bstrobel/Cass2SD/LTSpice/Cass2SD_AnalogStage.asc

C1: cap; 100n
C2: cap; 1n
C4: cap; 1.5p
C5: cap; 10p
C6: cap; 10p
D1: diode; 1N4148
D2: diode; 1N4148
R1: res; 15
R2: res; 1Meg
R3: res; 70k
R4: res; 30k
R5: res; 10Meg
R6: res; 100k
R7: res; 470
R8: res; 33k
R9: res; 13k
R11: res; 10Meg
U1: UniversalOpamp2; ""
U2: UniversalOpamp2; ""
V1: voltage; PULSE(3.2 0.2 2m 35n 35n .25m .5m 500); Rser=.5
V2: voltage; 5; Rser=.1
Named nets: 0, OUT, IN, NonInv_U1, TTL, Virtual_GND, VCC
.tran 0 100m 0m
.inc LM358.sub
Z9001 output circuit
1
2
3
5
6
7
8
4
ATMega input stage
