bstrobel/Cass2SD/main/kc_cass_common.c

/*
 * kc_cass_format_def.c
 *
 * Created: 06.06.2017 19:27:29
 *  Author: Bernd
 */ 
#define __PROG_TYPES_COMPAT__
#include <avr/pgmspace.h>
#include <avr/interrupt.h>
#include <avr/sfr_defs.h>
#include <stdbool.h>
#include <string.h>
#include <util/delay.h>
#include "../ff_avr/ff.h"
#include "../ff_avr/diskio.h"
#include "../ff_avr/xitoa.h"
#include "../lcd/lcd.h"
#include "debounced_keys.h"
#include "display_util.h"
#include "kc_cass_common.h"

DIR Dir;			/* http://elm-chan.org/fsw/ff/00index_e.html */
FILINFO Finfo;
FRESULT fr;
FATFS FatFs;		/* File system object for each logical drive */
FIL fhdl;

uint16_t disp_timer = 0;
bool is_file_details_displayed = false;

uint8_t* start_buf_ptr = buf;
uint8_t block_len = 128;
KC_FILE_TYPE kc_file_type = RAW;
uint8_t number_of_blocks = 0;

SYSTEM_STATE system_state = IDLE;

const char tap_header_str[] PROGMEM = "\xc3KC-TAPE by AF. ";

uint8_t buf[DATA_BUF_SIZE]; //send and receive buffer

/*---------------------------------------------------------*/
/* disk_and_debounce_timer                                 */
/* 100Hz timer interrupt generated by Timer2               */
/*---------------------------------------------------------*/
volatile uint8_t timer_cntr = 0;
ISR(TIMER2_COMPA_vect)
{
	if (timer_cntr++ > 39) {
		disk_timerproc();	/* Drive timer procedure of low level disk I/O module */
		timer_cntr=0;
	}
	handle_keys();
	disp_timer++;
}

void disk_and_debounce_timer_init (void)
{
	/* Start 3906.25Hz system timer with TC0 */
	// F=16MHz, prescaler=256 => 1 tick = 16µs
	// TOP=255 => max timer tick = 4096ms
	TCCR2A = _BV(WGM21); // CTC mode
	OCR2A = 15; // 16 * 16µs = 0.256ms => 3.90625kHz
	TCCR2B = _BV(CS22) | _BV(CS21); // 256 prescaler
	TIMSK2 = _BV(OCIE2A); // enable interrup at OC match A
}

uint8_t calculate_checksum() {
	uint8_t chksum = 0;
	for (uint8_t i = 1; i < (DATA_BUF_SIZE - 1); i++) {
		chksum += buf[i];
	}
	return chksum;
}


bool check_is_basic_fcb() {
	KC_FCB_BASIC* fcb_basic = (KC_FCB_BASIC*) (buf + 1);
	uint8_t b1 = fcb_basic->dateityp[0];
	uint8_t b2 = fcb_basic->dateityp[1];
	uint8_t b3 = fcb_basic->dateityp[2];
	return ( b1 >= 0xd3 && b1 <= 0xd9 && b1 == b2 && b1 == b3);
}

/************************************************************************/
/* Scans the file and checks if there are consecutive blocknrs          */
/* sets block_len=128, start_buf_prt = buf+1 if file has no blocknrs    */
/* sets block_len=129, start_buf_prt = buf if file provides blocknrs    */
/************************************************************************/
static bool detect_block_len() {
	// rewind to start of file
	if (disp_fr_err(f_lseek(&fhdl, 0))) {
		f_close(&fhdl);
		return false;
	}

	bool first_block = true;
	uint8_t last_blocknr = 0;
	UINT bytes_read;
	// Sweep through file and see if blocknumbers are consecutive
	while (1) {
		if (disp_fr_err(f_read(&fhdl, buf, BLOCK_LEN_WITH_BLOCKNUM, &bytes_read))) {
			f_close(&fhdl);
			return false;
		}

		if (bytes_read == BLOCK_LEN_WITHOUT_BLOCKNUM && first_block) {
			block_len = BLOCK_LEN_WITHOUT_BLOCKNUM;
			start_buf_ptr = buf + 1;
			break;
		}
		else if (bytes_read == 0 && !first_block) {
			break;
		}
		else if (bytes_read != BLOCK_LEN_WITH_BLOCKNUM && block_len == BLOCK_LEN_WITH_BLOCKNUM) {
			// this shouldn't happen, this is an error!
			f_close(&fhdl);
			return false;
		}

		if (first_block) {
			if (buf[0] < 2) {
				// Normal files start with block=0, BASIC files with block=1
				last_blocknr = buf[0];
				start_buf_ptr = buf;
				block_len = BLOCK_LEN_WITH_BLOCKNUM;
			}
			else {
				// already the first blocknr is wrong, so we dont have blocknrs
				start_buf_ptr = buf + 1;
				block_len = BLOCK_LEN_WITHOUT_BLOCKNUM;
				break;
			}
			first_block = false;
		}
		else {
			if (buf[0] == last_blocknr + 1 || buf[0] == 0xff) // 0xff blocks are allowed
			last_blocknr = buf[0];
			// we have set start_buf_ptr and block_len in the first_block part already
			else {
				// no consecutive blocknr -> we assume no blocknrs
				start_buf_ptr = buf + 1;
				block_len = BLOCK_LEN_WITHOUT_BLOCKNUM;
				break;
			}
		}

	}
	// rewind again
	if (disp_fr_err(f_lseek(&fhdl, 0))) {
		f_close(&fhdl);
		return false;
	}
	return true;
}

static bool create_fcb_from_filename(FILINFO* Finfo) {
	KC_FCB* fcb = (KC_FCB*) (start_buf_ptr);
	memset(buf,0x0,DATA_BUF_SIZE);
	int8_t dot_index = -1;
	uint8_t fname_idx=0;
	bool end_reached = false;
	for (uint8_t i = 0; i < LEN_DATEINAME; i++, fname_idx++) {
		if (Finfo->fname[fname_idx] == 0) {
			end_reached = true;
		}
		if (dot_index < 0 && Finfo->fname[i] == '.') {
			dot_index = i;
		}
		if (dot_index >= 0 || end_reached) {
			fcb->dateiname[i] = 0x20;
		}
		else {
			fcb->dateiname[i] = Finfo->fname[fname_idx];
		}
	}
	if (dot_index < 0) {
		// still no dot, so it must be there at the current fname_idx -> skipping
		fname_idx++;
	}
	for (uint8_t i = 0; i<LEN_DATEITYP; i++, fname_idx++) {
		if (Finfo->fname[fname_idx] == 0) {
			end_reached = true;
		}
		if (end_reached) {
			fcb->dateityp[i] = 0x20;
		}
		else {
			fcb->dateityp[i] = Finfo->fname[fname_idx];
		}
	}
	#define AADR 0x0200
	fcb->aadr_L = AADR % 0x100;
	fcb->aadr_H = AADR / 0x100;
	number_of_blocks = (uint8_t)((Finfo->fsize / block_len) + 1);
	if (HAS_NO_BLOCKNR) {
		fcb->eadr_L = (uint8_t)(AADR + Finfo->fsize);
		fcb->eadr_H = (uint8_t)((AADR + Finfo->fsize) >> 8);
	}
	else {
		fcb->eadr_L = (uint8_t)(AADR + Finfo->fsize - number_of_blocks);
		fcb->eadr_H = (uint8_t)((AADR + Finfo->fsize - number_of_blocks) >> 8);
	}
	fcb->sadr_H = 0;
	fcb->sadr_L = 0;
	fcb->byte_18 = FCB_BYTE18_NOSTART;
	// Finally we rewind the file to the beginning
	if (disp_fr_err(f_lseek(&fhdl, 0))) {
		f_close(&fhdl);
		return false;
	}
	return true;
}

static bool check_non_tap_types(FILINFO* Finfo) {
	// non-TAP files may have the block numbers in the file or not
	// this determines the block_len:
	//  129 with blocknr
	//  128 without blocknr
	if(!detect_block_len()) {
		return false;
	}

	// load the first block completely
	// start_buf_ptr and block_len are now correct
	UINT bytes_read;
	if (disp_fr_err(f_read(&fhdl, start_buf_ptr, block_len, &bytes_read))) {
		f_close(&fhdl);
		return false;
	}

	// check if BASIC FCB
	if (check_is_basic_fcb()) {
		// BASIC FCB found
		kc_file_type = BASIC_W_HEADER;
		number_of_blocks = (uint8_t)(Finfo->fsize / block_len);
		if (HAS_NO_BLOCKNR) {
			buf[0] = 1; // BASIC files start with block #1
		}
		return true;
	}

	// check the file extension if it is of BASIC type ('SSS','TTT',...)
	char* ext = strchr(Finfo->fname,'.') + 1;
	for (uint8_t c = 0x53; c <= 0x59; c++) { // stepping through from 'S' to 'Y'
		if (ext[0] == c && ext[1] == c && ext[2] == c) {
			kc_file_type = BASIC_NO_HEADER; // -> we found a BASIC file ext.
			// Create the BASIC FCB
			start_buf_ptr[0] = c + 0x80; // set the magic 3 letter header (0xd3d3d3, 0xd4d4d4, ...)
			start_buf_ptr[1] = c + 0x80;
			start_buf_ptr[2] = c + 0x80;
			// Copy the filename in the header
			for (uint8_t i=0; i < 8; i++) {
				if (Finfo->fname + i < (ext - 1)) {
					start_buf_ptr[i+3] = Finfo->fname[i];
				}
				else {
					start_buf_ptr[i+3] = 0x20;
				}
			}
			// reload the file contents after the just created header
			if (disp_fr_err(f_lseek(&fhdl, 0))) {
				f_close(&fhdl);
				return false;
			}
			uint8_t bytes_to_read = block_len - BASIC_HEADER_LEN;
			if (disp_fr_err(f_read(&fhdl, start_buf_ptr + BASIC_HEADER_LEN, bytes_to_read, &bytes_read))) {
				f_close(&fhdl);
				return false;
			}
			if (bytes_read != bytes_to_read) {
				disp_msg_p(msg_error_str,msg_block_too_short_str);
				return false;
			}
			number_of_blocks = (uint8_t)((Finfo->fsize + BASIC_HEADER_LEN) / block_len);
			if (HAS_NO_BLOCKNR) {
				buf[0] = 1; // BASIC files start with block #1
			}
			return true;
		}
	}

	if (HAS_NO_BLOCKNR) {
		buf[0] = 0; // initialize the blocknr if not provided
	}
	
	// No BASIC FCB and no BASIC extension, now check for regular FCB header
	KC_FCB* fcb = (KC_FCB*) (start_buf_ptr);
	for (uint8_t j=0; j < LEN_DATEINAME; j++) {
		// We accept 0x0 bytes in the dateiname and dateityp area of FCB, but the first character must not be 0!
		if (fcb->dateiname[0] == 0 || (fcb->dateiname[j] > 0 && fcb->dateiname[j] < 0x20) || fcb->dateiname[j] < 0)  {
			// found unprintable character -> cannot be a real fcb
			kc_file_type = RAW;
			return create_fcb_from_filename(Finfo);
		}
	}
	for (uint8_t j=0; j < LEN_DATEITYP; j++) {
		if ((fcb->dateityp[j] > 0 && fcb->dateityp[j] < 0x20) || fcb->dateityp[j] < 0)  {
			// found unprintable character -> cannot be a real fcb
			kc_file_type = RAW;
			return create_fcb_from_filename(Finfo);
		}
	}
	// we found a valid FCB but dont know what it is.
	kc_file_type = OTHER_THAN_BASIC;
	number_of_blocks = (uint8_t)(Finfo->fsize / block_len);
	return true;
}

static bool check_tap_types(FILINFO* Finfo) {
	kc_file_type = TAP;
	
	number_of_blocks = (uint8_t)((Finfo->fsize - TAP_HEADER_LEN) / 129);
	
	// read the first block after the TAP_HEADER
	UINT bytes_read;
	if (disp_fr_err(f_lseek(&fhdl, TAP_HEADER_LEN)) || disp_fr_err(f_read(&fhdl, start_buf_ptr, block_len, &bytes_read))) {
		f_close(&fhdl);
		return false;
	}

	if (check_is_basic_fcb()) {
		kc_file_type = TAP_BASIC;
	}
	else {
		// workaround for TAP files that contain a meaningless block 0 before the
		// actual first BASIC block #1. We remove it. We also replace will replace
		// the block number of block #255 with a consecutive number later.
		// so load the first block after the header and see if it is BASIC
		if (disp_fr_err(f_read(&fhdl, start_buf_ptr, block_len, &bytes_read))) {
			f_close(&fhdl);
			return false;
		}
		if (check_is_basic_fcb()) {
			// BASIC header found
			kc_file_type = TAP_BASIC_EXTRA_BLOCKS;
			number_of_blocks--;
		}
		else
		{
			// it is not BASIC
			// rewind to beginning of first block after TAP header and reload
			if (disp_fr_err(f_lseek(&fhdl, TAP_HEADER_LEN)) ||
			disp_fr_err(f_read(&fhdl, start_buf_ptr, block_len, &bytes_read))) {
				f_close(&fhdl);
				return false;
			}
		}
	}
	return true;
}

bool load_first_block_and_check_type(FILINFO* Finfo) {
	block_len = 129;
	start_buf_ptr = buf;
	if (Finfo->fsize < 128) { // file too short -> we don't even care to look further
		lcd_clrscr();
		xprintf(PSTR("ERR:%s"),Finfo->fname);
		lcd_gotoxy(0,1);
		xprintf(PSTR("Too short:%ub"),Finfo->fsize);
		_delay_ms(ERROR_DISP_MILLIS);
		return false;
	}
	if (disp_fr_err(f_open(&fhdl, Finfo->fname, FA_READ | FA_OPEN_EXISTING))) {
		f_close(&fhdl);
		return false;
	}
	// load first TAP_HEADER_LEN to check for TAP header
	UINT bytes_read;
	if (disp_fr_err(f_read(&fhdl, buf, TAP_HEADER_LEN, &bytes_read))) {
		f_close(&fhdl);
		return false;
	}

	if (strncmp_P((char*)buf,tap_header_str,bytes_read)) {
		return check_non_tap_types(Finfo);
	}
	else {
		return check_tap_types(Finfo);
	}
	return true;
}
