bstrobel/Cass2SD/main/kc_cass_common.h

/*
 * kc_cass_format_def.h
 *
 * Created: 03.06.2017 14:51:38
 *  Author: Bernd
 */ 


#ifndef KC_CASS_FORMAT_DEF_H_
#define KC_CASS_FORMAT_DEF_H_

#include <stdint.h>
#include <stdbool.h>
#define __PROG_TYPES_COMPAT__
#include <avr/pgmspace.h>
#include "../ff_avr/ff.h"

extern DIR Dir;			/* http://elm-chan.org/fsw/ff/doc/sdir.html */
extern FILINFO Finfo; /* http://elm-chan.org/fsw/ff/doc/sfileinfo.html */
extern FRESULT fr;
extern FATFS FatFs;		/* File system object for each logical drive */
extern FIL fhdl;

extern uint16_t disp_timer;
extern bool is_file_details_displayed;
#define DISP_FILE_DETAILS_TIMEOUT_COUNT 12000U


extern uint8_t* start_buf_ptr;
extern uint8_t block_len;
extern uint8_t number_of_blocks;

typedef enum
{
	BASIC_NO_HEADER,
	BASIC_W_HEADER,
	OTHER_THAN_BASIC,
	RAW,
	TAP,
	TAP_BASIC,
	TAP_BASIC_EXTRA_BLOCKS
} KC_FILE_TYPE;

extern KC_FILE_TYPE kc_file_type;

typedef enum {
	IDLE=0,
	SENDING,
	RECEIVING
} SYSTEM_STATE;

extern SYSTEM_STATE system_state;

#define DATA_BUF_SIZE 130
extern uint8_t buf[];

#define BLOCK_LEN_WITH_BLOCKNUM 129
#define BLOCK_LEN_WITHOUT_BLOCKNUM 128
#define HAS_NO_BLOCKNR (block_len == BLOCK_LEN_WITHOUT_BLOCKNUM)

#define TYPE_IS_BASIC ( \
kc_file_type == TAP_BASIC \
|| kc_file_type == TAP_BASIC_EXTRA_BLOCKS \
|| kc_file_type == BASIC_NO_HEADER \
|| kc_file_type == BASIC_W_HEADER \
)

#define TYPE_IS_BASIC_WITH_HEADER ( \
kc_file_type == TAP_BASIC \
|| kc_file_type == TAP_BASIC_EXTRA_BLOCKS \
|| kc_file_type == BASIC_W_HEADER \
)

#define TYPE_IS_WITH_HEADER_NO_BASIC ( \
kc_file_type == OTHER_THAN_BASIC \
|| kc_file_type == TAP \
)

#define TYPE_IS_NO_HEADER ( \
kc_file_type == RAW \
)

typedef enum {SPACE=0, ONE, ZERO} BIT_TYPE;

extern const char tap_header_str[] PROGMEM;
#define TAP_HEADER_LEN 16

#define LEN_DATEINAME 8
#define LEN_DATEITYP 3

#define FCB_BYTE18_NOSTART 0x02
#define FCB_BYTE18_START_RELOCATE 0x03
#define FCB_BYTE18_START_NORELOCATE4 0x04
#define FCB_BYTE18_START_NORELOCATE5 0x05
#define FCB_BYTE18_START_NORELOCATE6 0x06
#define FCB_BYTE18_START_NORELOCATE7 0x07

typedef struct{
	char dateiname[LEN_DATEINAME]; // NOT null terminated file name, filled with 0x20 if shorter than 8 characters
	char dateityp[LEN_DATEITYP]; // same as dateiname[]
	uint8_t ext1;
	uint8_t ext2;
	uint8_t psum;
	uint8_t arb;
	uint8_t blnr;
	 // byte_18 is special for KC85/3 (source - KC85/3 Systemhandbuch):
	 // 0x02 -> only load, no start, sadr_L + sadr_H can be 0
	 // 0x03 -> start after load, recalculate start address if loaded relatively
	 // 0x04..0x07 -> start after load, no recalculation of start address if loaded relatively
	uint8_t byte_18;
	uint8_t aadr_L;
	uint8_t aadr_H;
	uint8_t eadr_L;
	uint8_t eadr_H;
	uint8_t sadr_L;
	uint8_t sadr_H;
	uint8_t sby;
} KC_FCB;

typedef struct
{
	char dateityp[LEN_DATEITYP];
	char dateiname[LEN_DATEINAME];
} KC_FCB_BASIC;
#define BASIC_HEADER_LEN (LEN_DATEINAME + LEN_DATEITYP)

#define VORTON_BEGIN 6000
#define VORTON_BLOCK 160
#define VORTON_FFBLOCK 5296

uint8_t calculate_checksum(void);
bool check_is_basic_fcb(void);
void disk_and_debounce_timer_init (void);
bool load_first_block_and_check_type(FILINFO* Finfo);
#endif /* KC_CASS_FORMAT_DEF_H_ */
